rajatchaple/ecen5833_s22_lpedt_project/images/20220211_230712.jpg

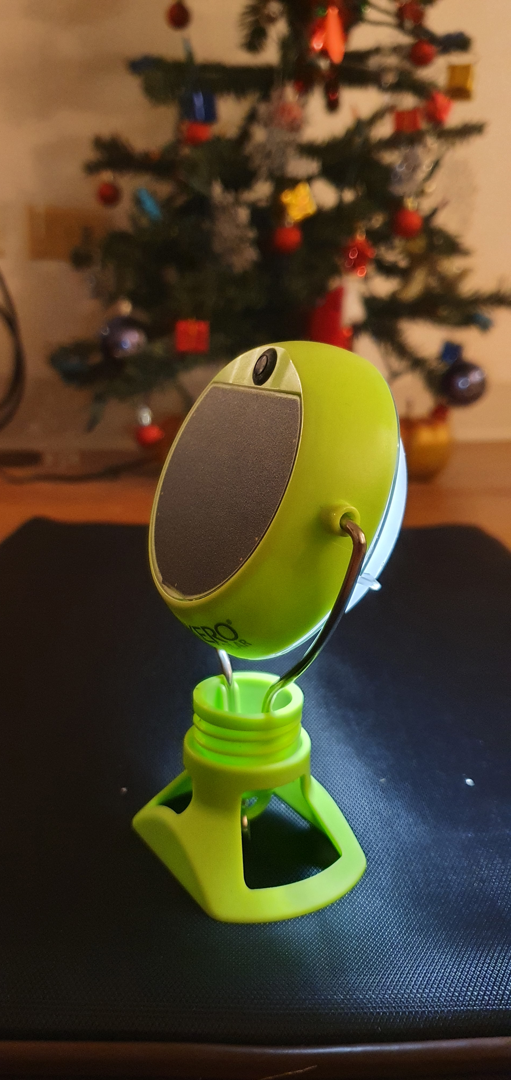
images/20220211_230712.jpg
