rajatchaple/ecen5833_s22_lpedt_project/images/20220218_140802.jpg

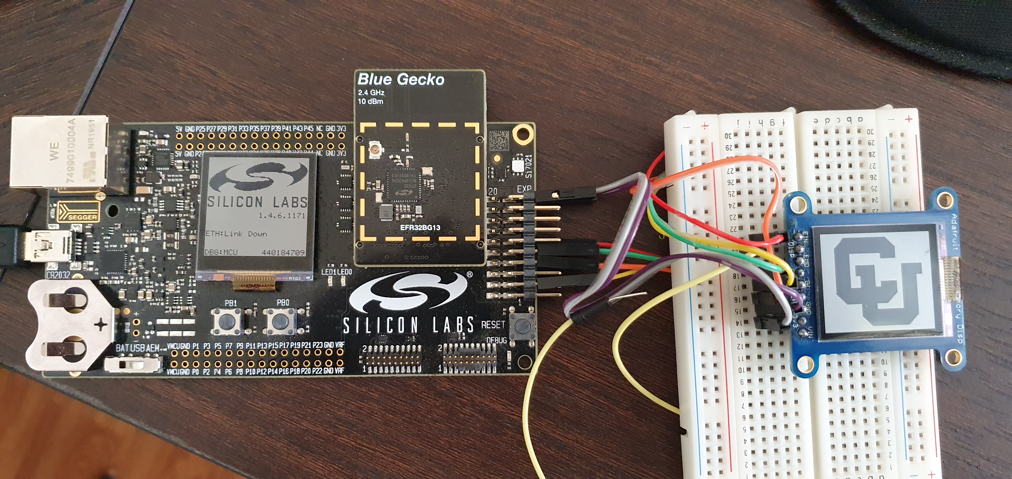
images/20220218_140802.jpg
