rajatchaple/ecen5833_s22_lpedt_project/images/20220218_140817.jpg

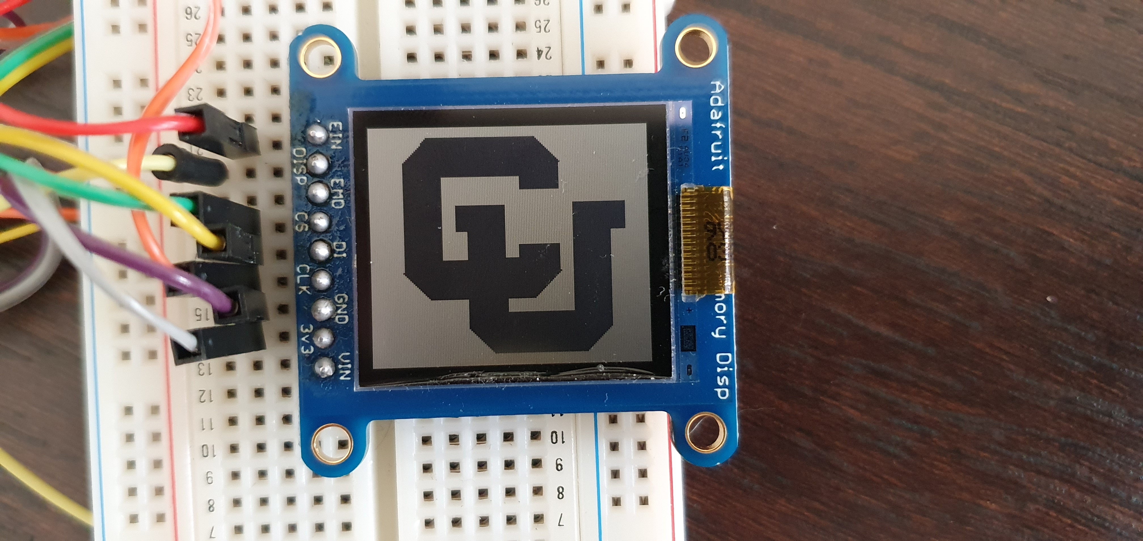
images/20220218_140817.jpg
