rajatchaple/ecen5833_s22_lpedt_project/images/20220219_193055.jpg

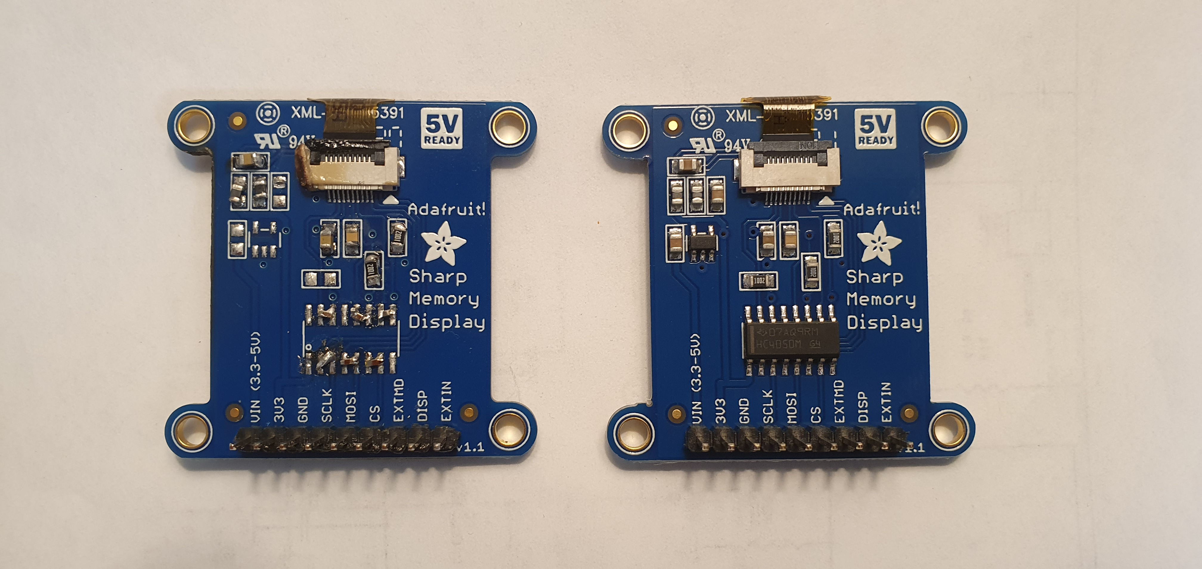
images/20220219_193055.jpg
