rajatchaple/ecen5833_s22_lpedt_project/images/20220226_095113.jpg

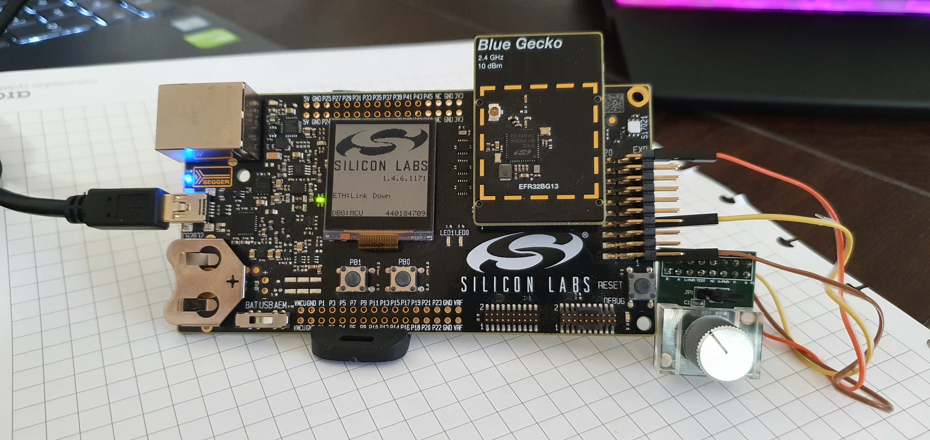
images/20220226_095113.jpg
