rajatchaple/ecen5833_s22_lpedt_project/images/bulk_cap.png

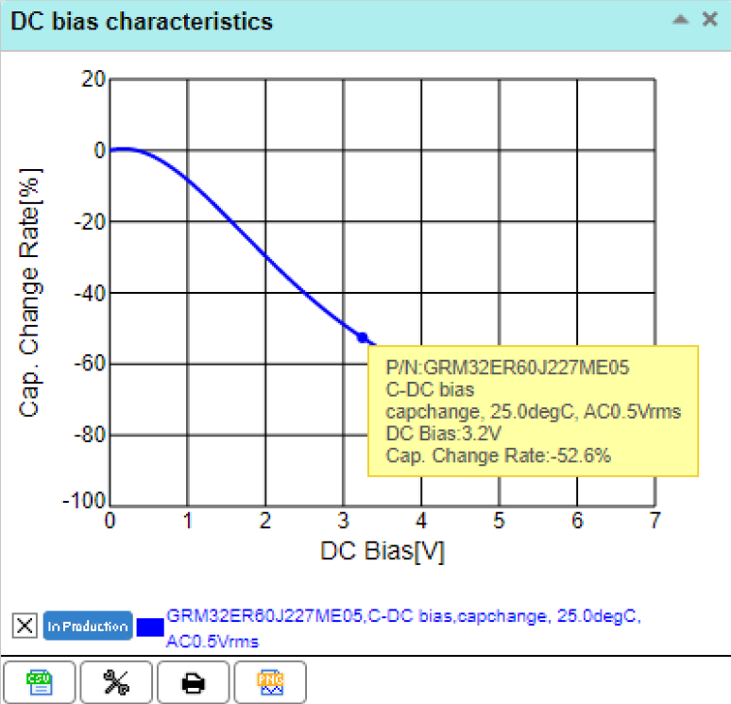
images/bulk_cap.png
