rajatchaple/ecen5833_s22_lpedt_project/images/imu_i2c.png

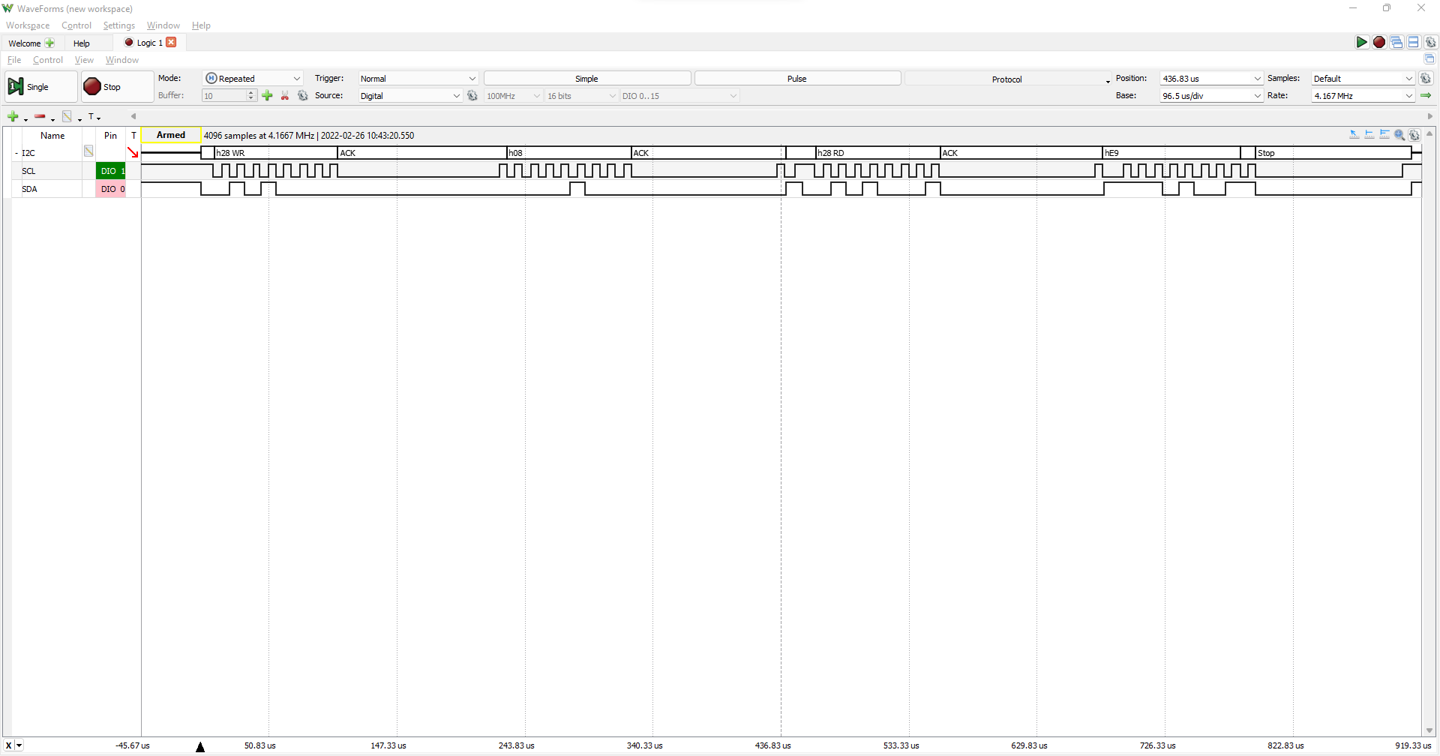
images/imu_i2c.png
