rajatchaple/ecen5833_s22_lpedt_project/images/lcd.jpg

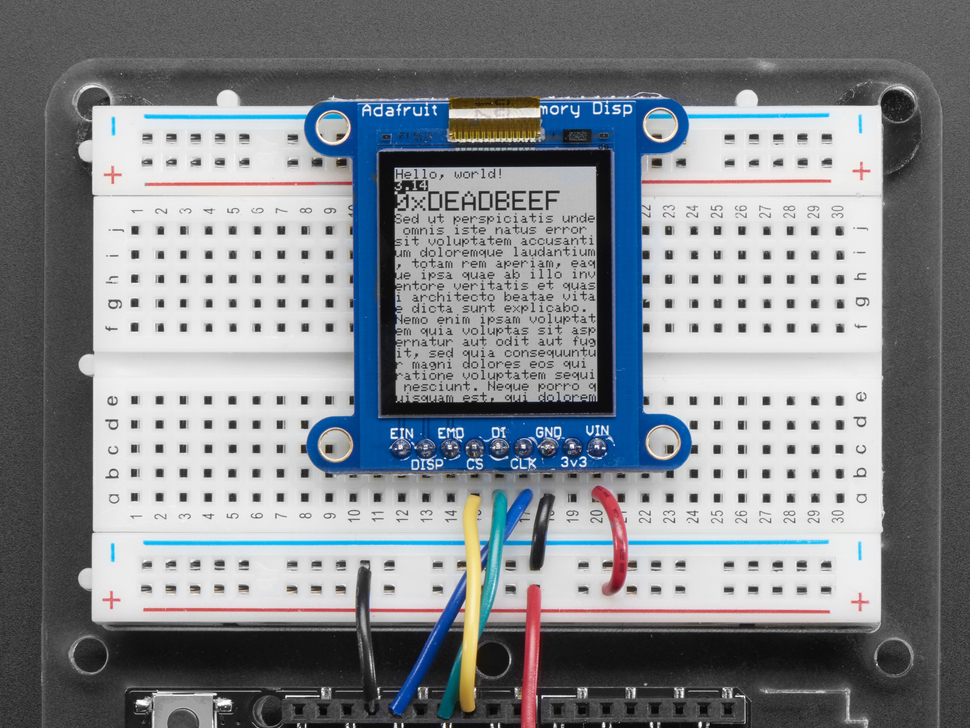
images/lcd.jpg
