rajatchaple/ecen5833_s22_lpedt_project/images/ltspice.png

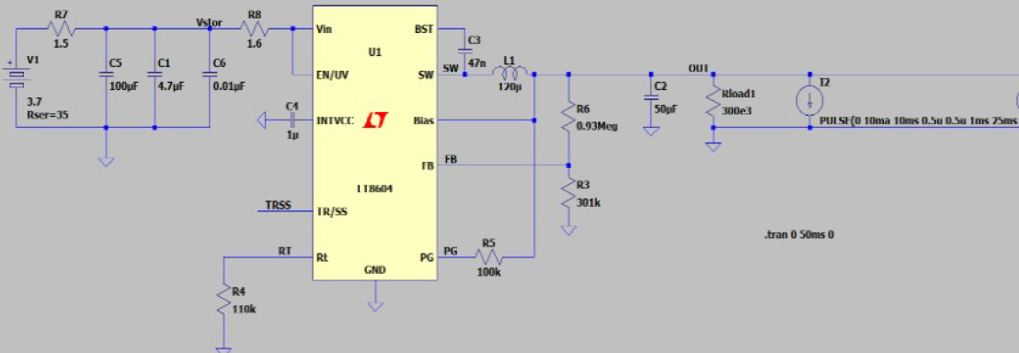
images/ltspice.png
