rajatchaple/ecen5833_s22_lpedt_project/images/ltspice_graph.png

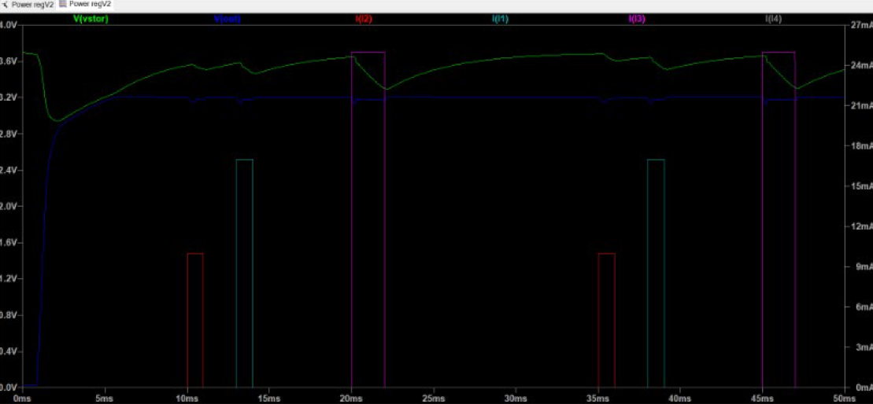
images/ltspice_graph.png
