rajatchaple/ecen5833_s22_lpedt_project/images/mag enc arduino pwm 2.png

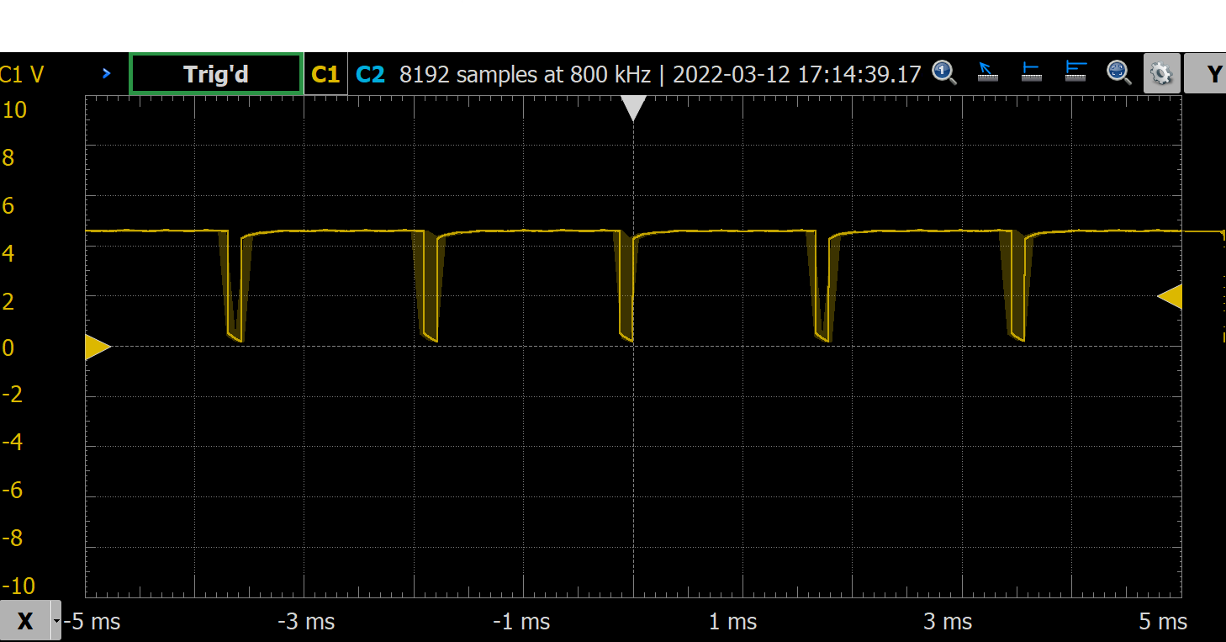
images/mag enc arduino pwm 2.png
