rajatchaple/ecen5833_s22_lpedt_project/images/mag enc arduino pwm 3.png

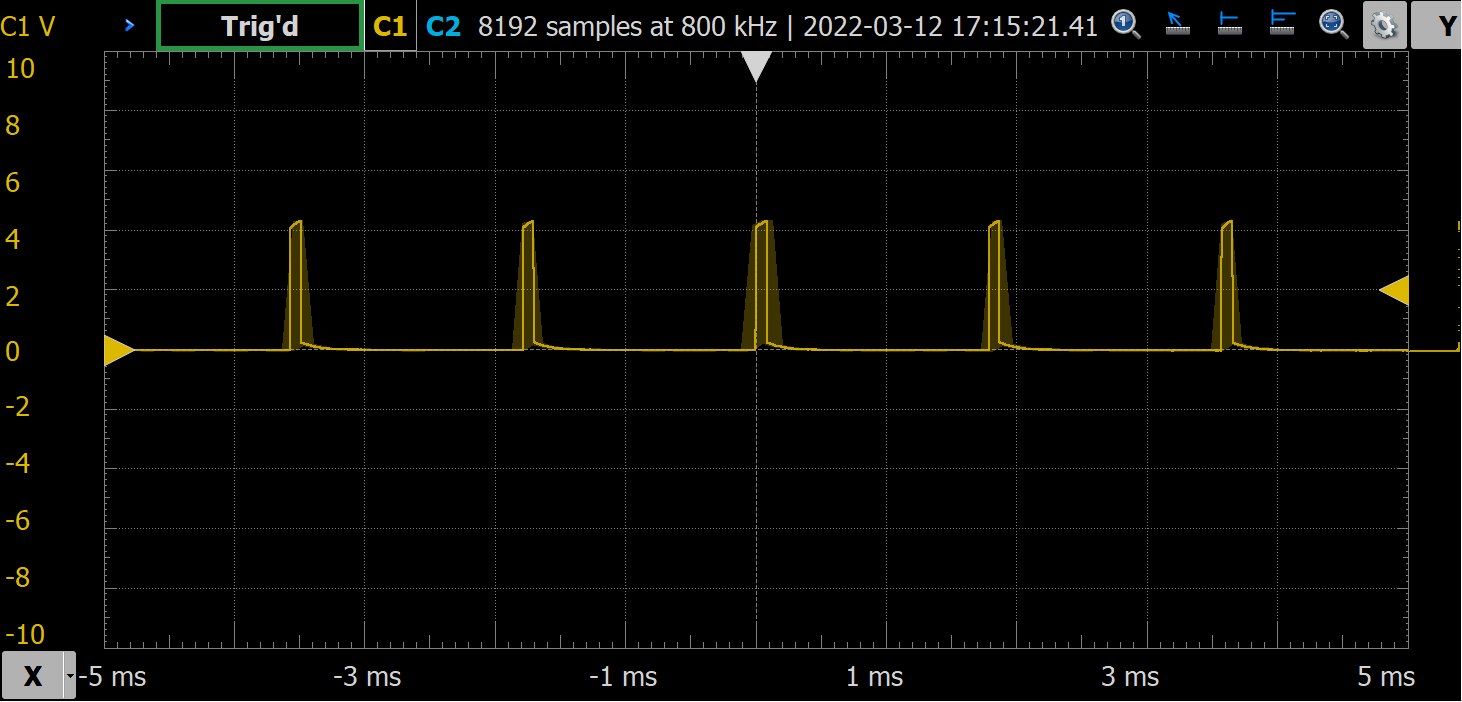
images/mag enc arduino pwm 3.png
