rajatchaple/ecen5833_s22_lpedt_project/images/Magnetic Encoder energy profile.png

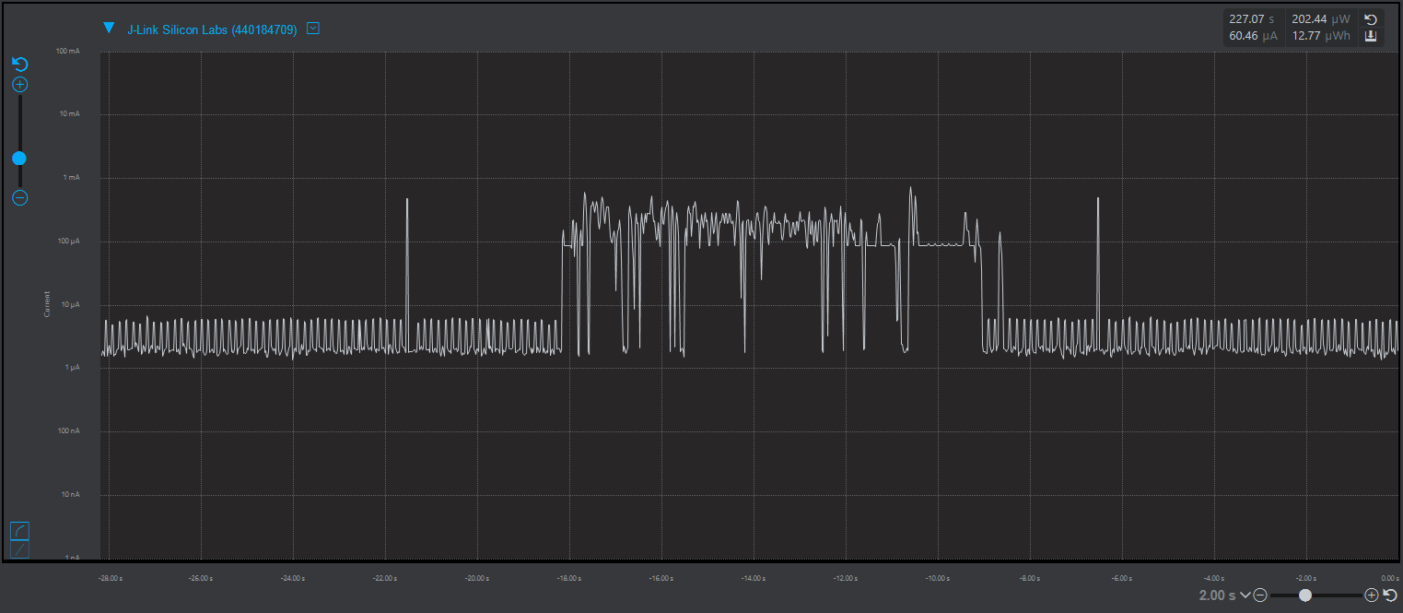
images/Magnetic Encoder energy profile.png
