rajatchaple/ecen5833_s22_lpedt_project/images/Magnetic Encoder pulses on serial.png

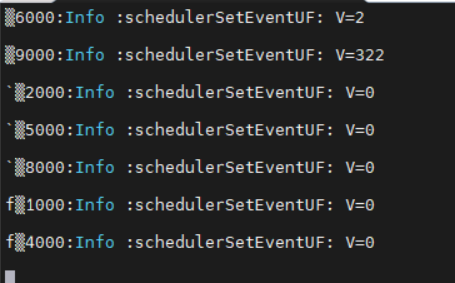
images/Magnetic Encoder pulses on serial.png
