rajatchaple/ecen5833_s22_lpedt_project/images/Magnetic Encoder pulses on serial_mod.jpg

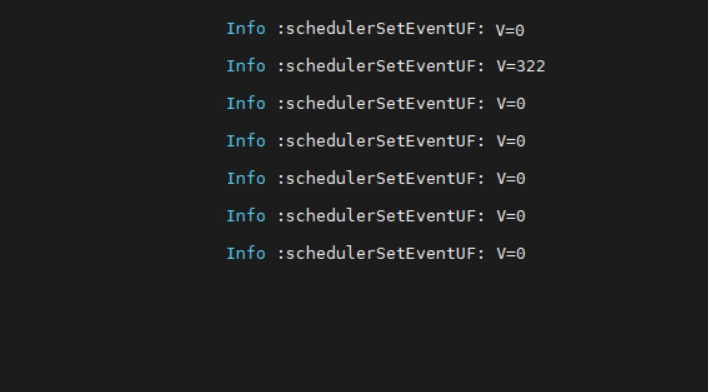
images/Magnetic Encoder pulses on serial_mod.jpg
