rajatchaple/ecen5833_s22_lpedt_project/images/magnetIc_encoder.png

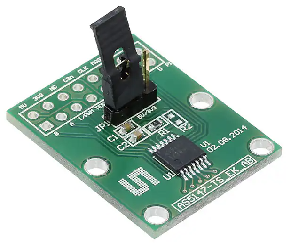
images/magnetIc_encoder.png
