rajatchaple/ecen5833_s22_lpedt_project/images/PowerTrace.png

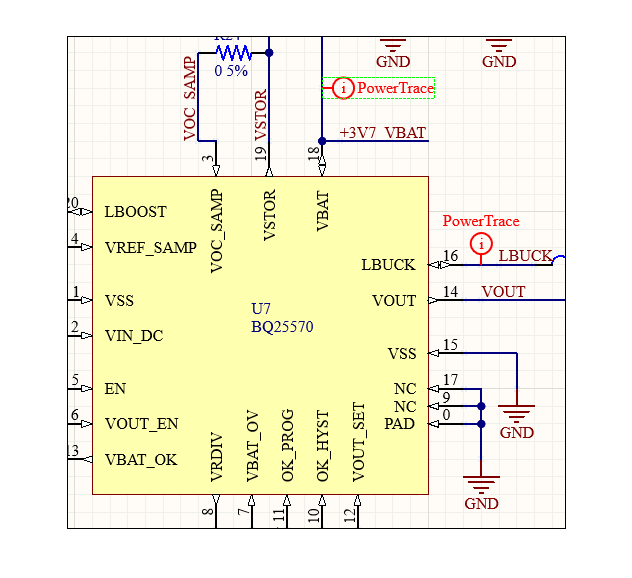
images/PowerTrace.png
