rajatchaple/ecen5833_s22_lpedt_project/images/Screenshot_20220219-193332_WhatsApp.jpg

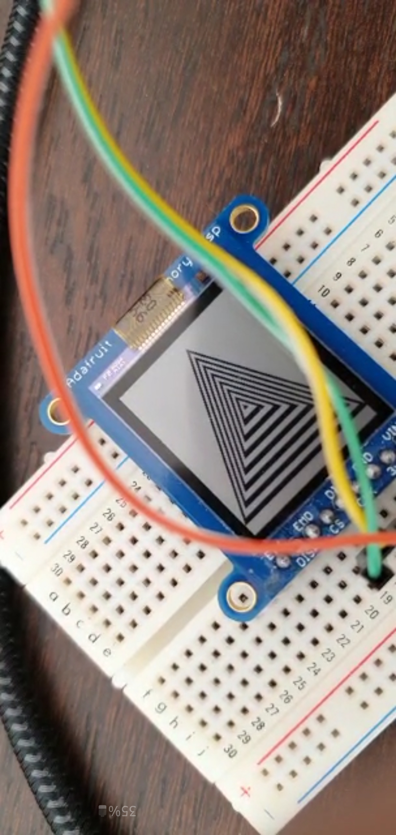
images/Screenshot_20220219-193332_WhatsApp.jpg
