rajatchaple/ecen5833_s22_lpedt_project/images/subcomponents.png

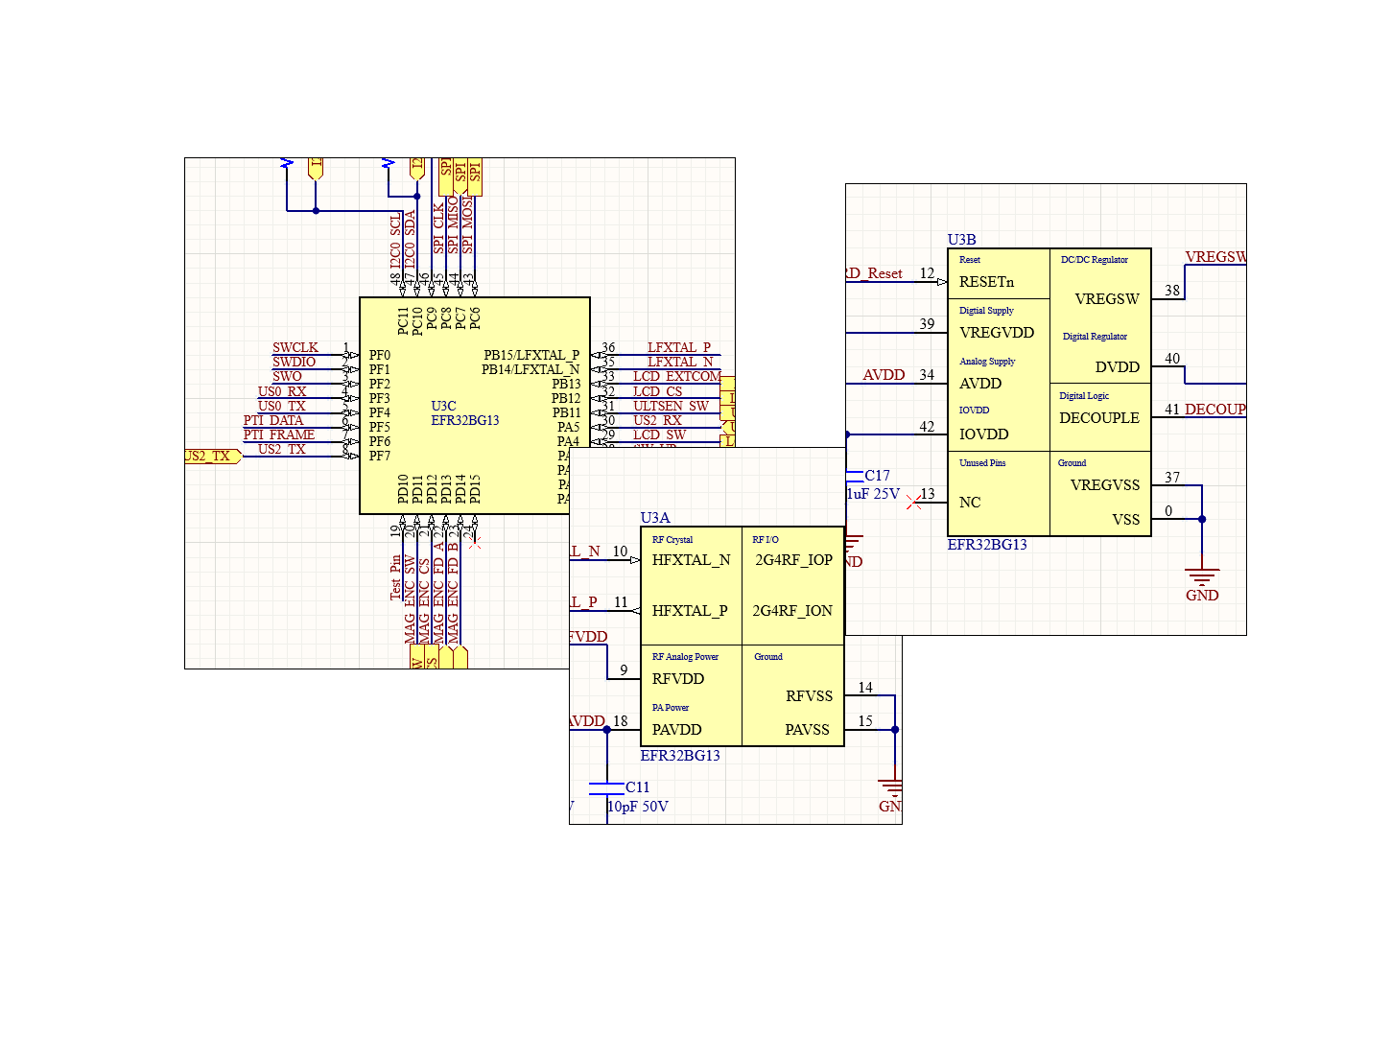
images/subcomponents.png
