rajatchaple/ecen5833_s22_lpedt_project/images/T_junctions.png

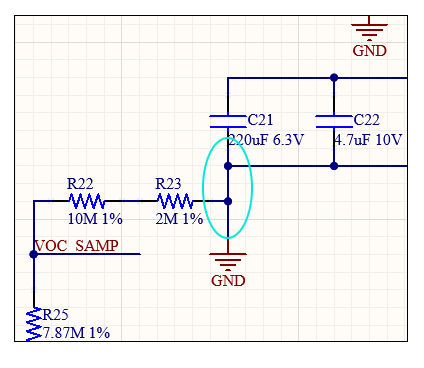
images/T_junctions.png
