rajatchaple/ecen5833_s22_lpedt_project/images/ultrasonic.jpg

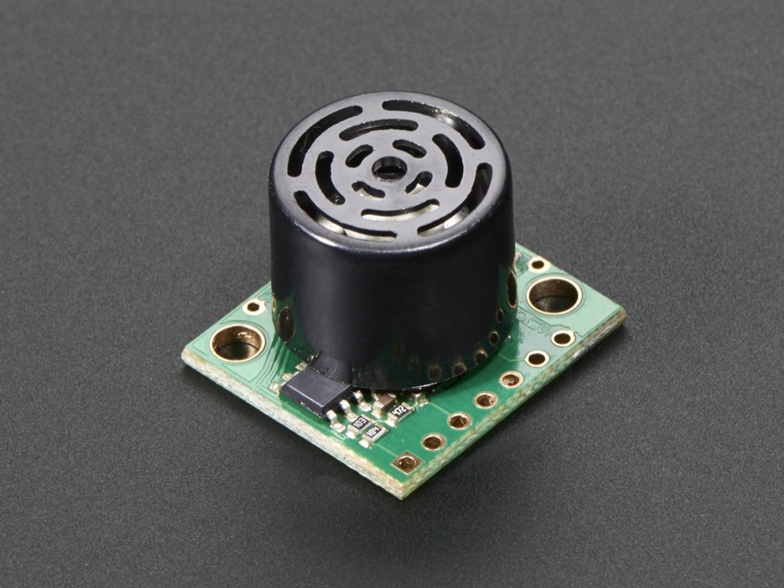
images/ultrasonic.jpg
