rajatchaple/ecen5833_s22_lpedt_project/software/software_ultrasonic/readme_img0.png

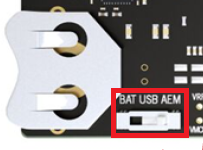
software/software_ultrasonic/readme_img0.png
