rajatchaple/ecen5833_s22_lpedt_project/software/software_ultrasonic/readme_img2.png

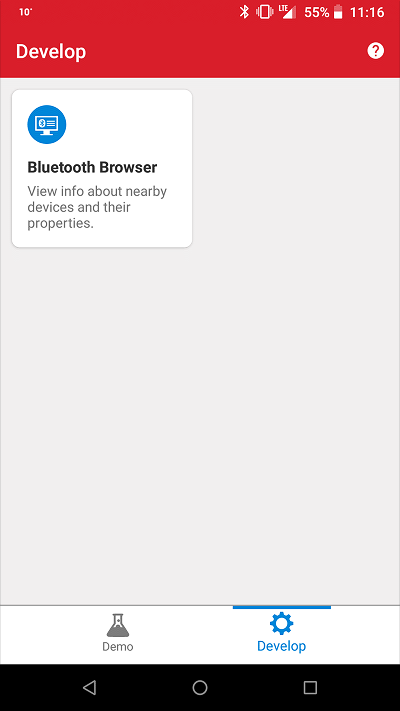
software/software_ultrasonic/readme_img2.png
