rajatchaple/ecen5833_s22_lpedt_project/software/source/readme_img1.jpg

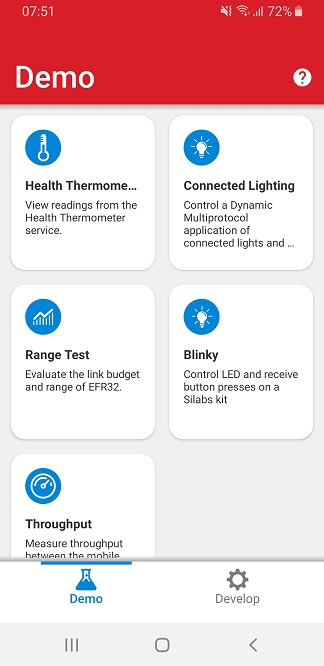
software/source/readme_img1.jpg
