rajatchaple/ecen5833_s22_lpedt_project/software/source/readme_img3.jpg

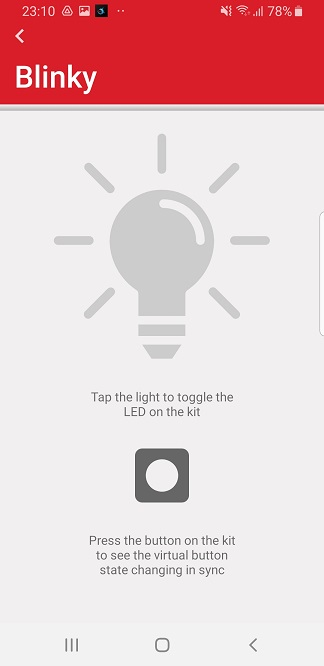
software/source/readme_img3.jpg
