rajatchaple/ecen5833_s22_lpedt_project/software/source/readme_img5.gif

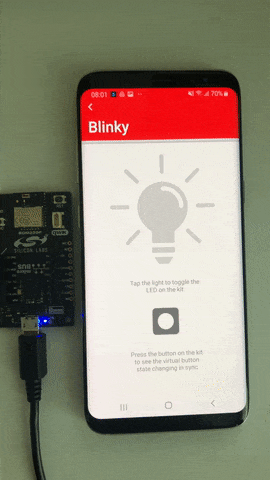
software/source/readme_img5.gif
