rajatchaple/ecen5833_s22_lpedt_project/utilities/LCD/CU.png

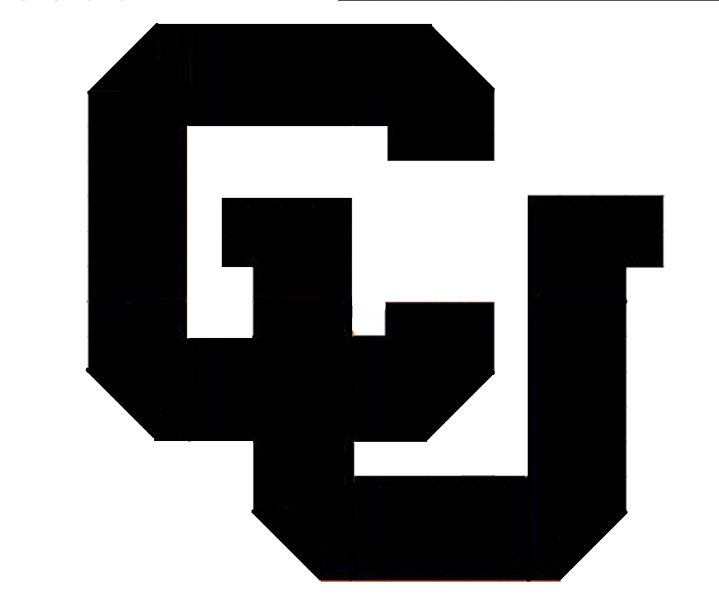
utilities/LCD/CU.png
