rajatchaple/ecen5833_s22_lpedt_project/utilities/LCD/ff.png

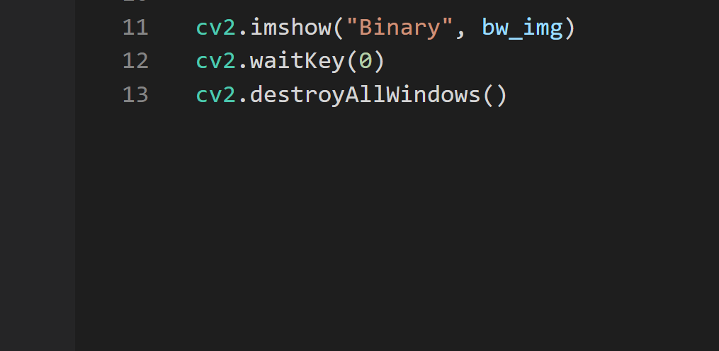
utilities/LCD/ff.png
